pwestman/pwestman.github.io/Images/ghmain.JPG

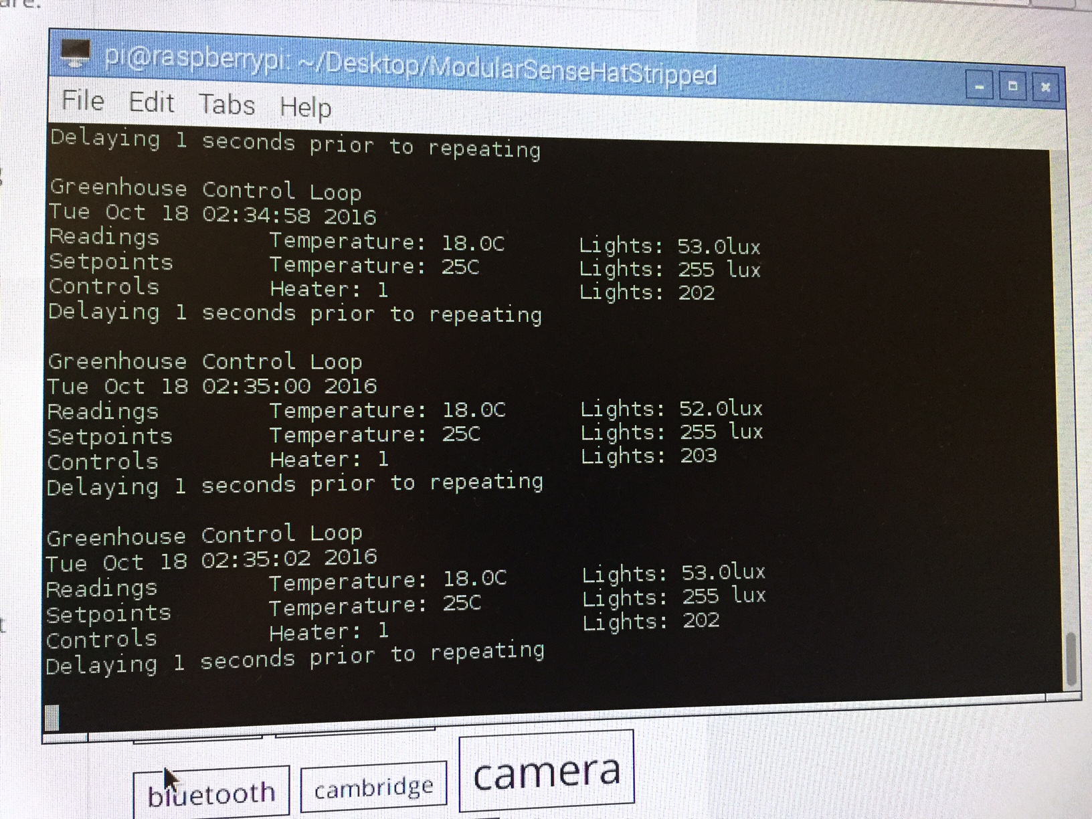
Images/ghmain.JPG
