pwestman/pwestman.github.io/Images/green.jpg

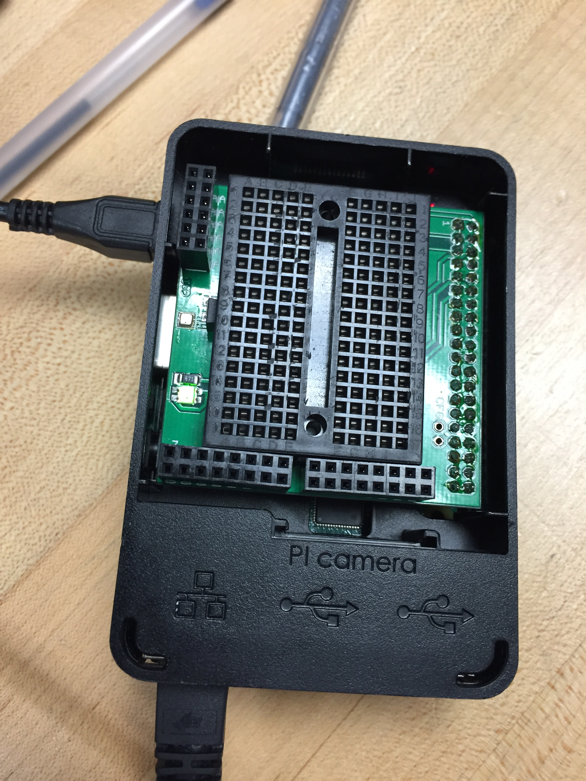
Images/green.jpg
