pwestman/pwestman.github.io/Images/greenLight.JPG

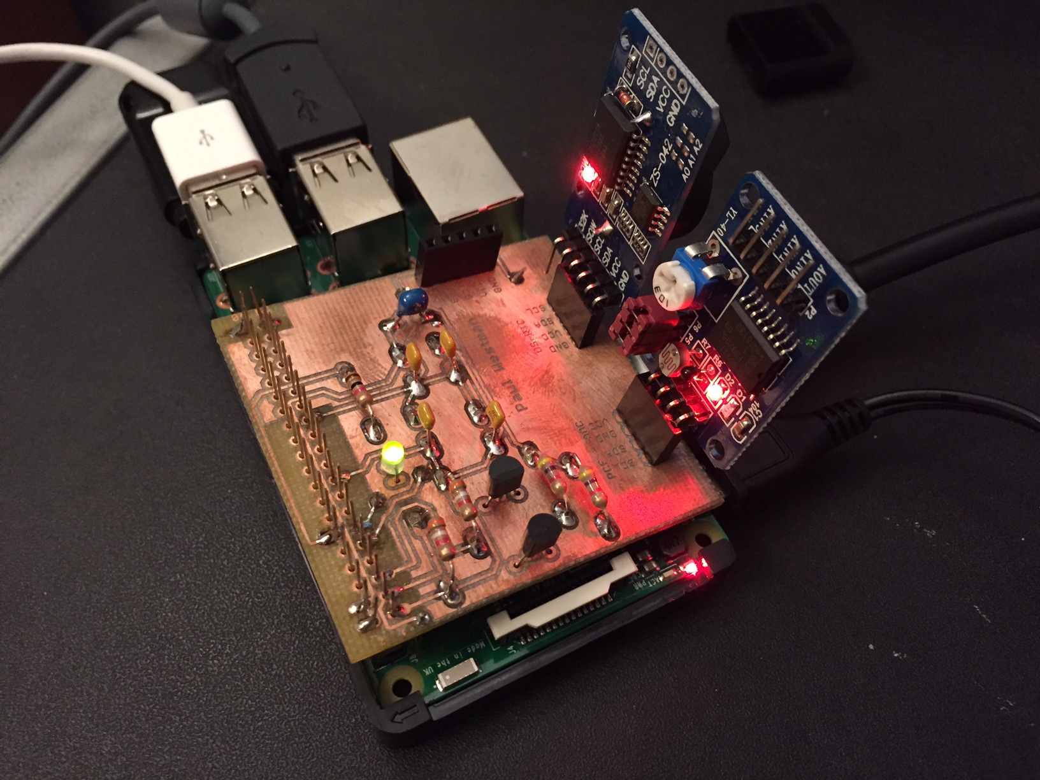
Images/greenLight.JPG
