pwestman/pwestman.github.io/Images/i2cdetect.JPG

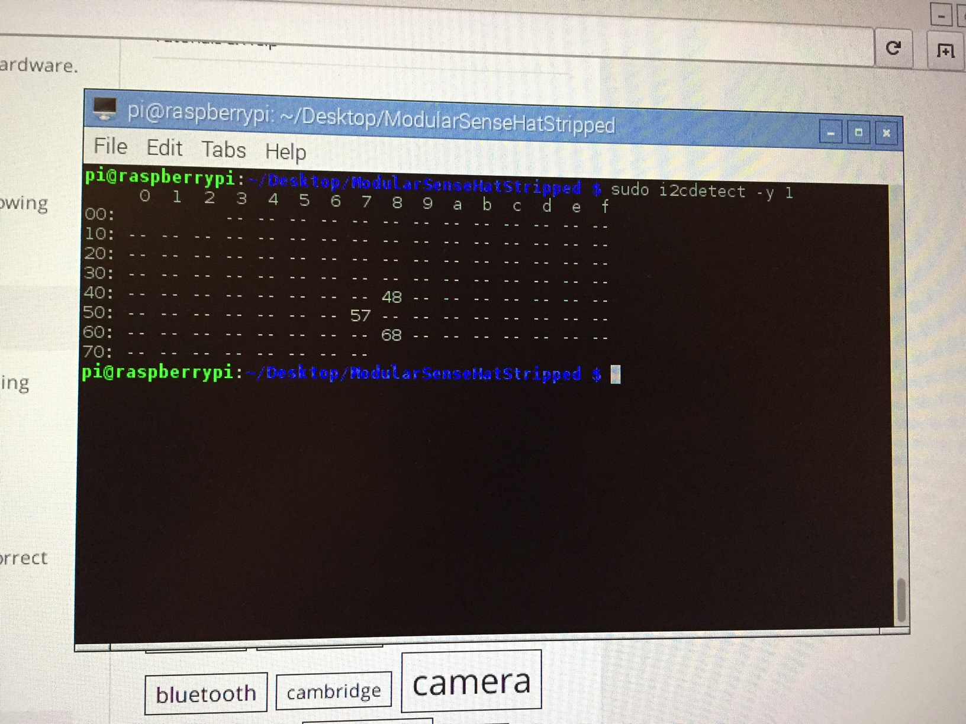
Images/i2cdetect.JPG
