pwestman/pwestman.github.io/Images/PCB.JPG

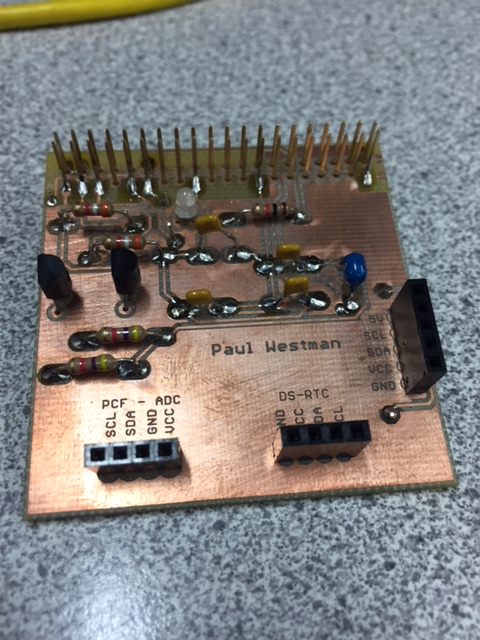
Images/PCB.JPG
