pwestman/pwestman.github.io/Images/traffic2B.JPG

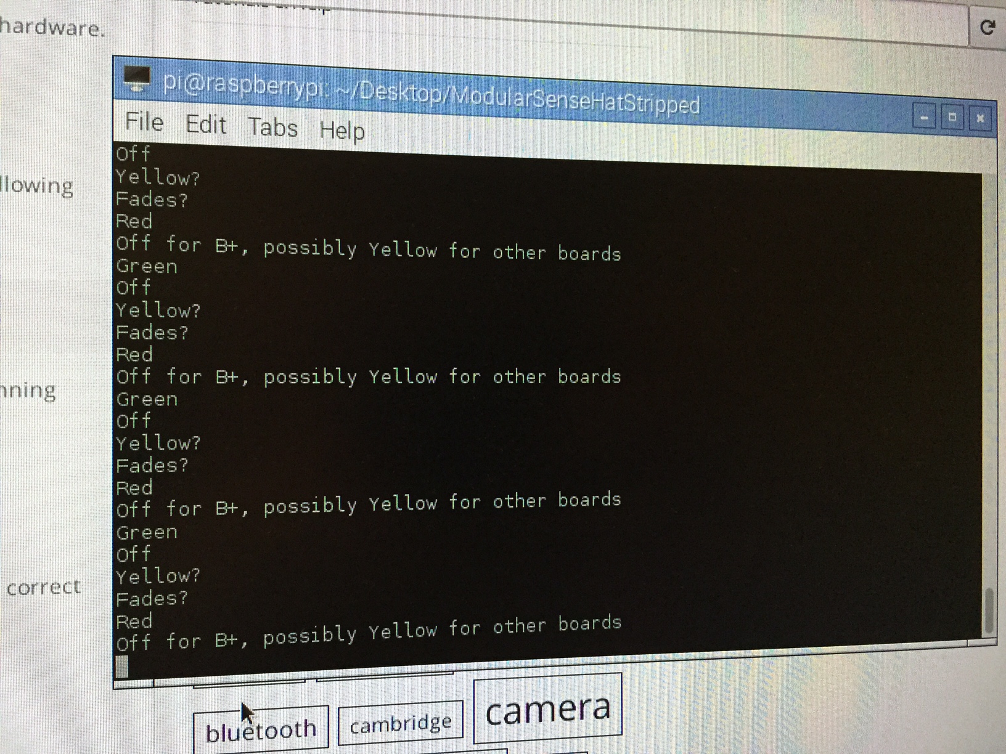
Images/traffic2B.JPG
