pwestman/pwestman.github.io/README.images/AcrylicScaleWalls.jpg

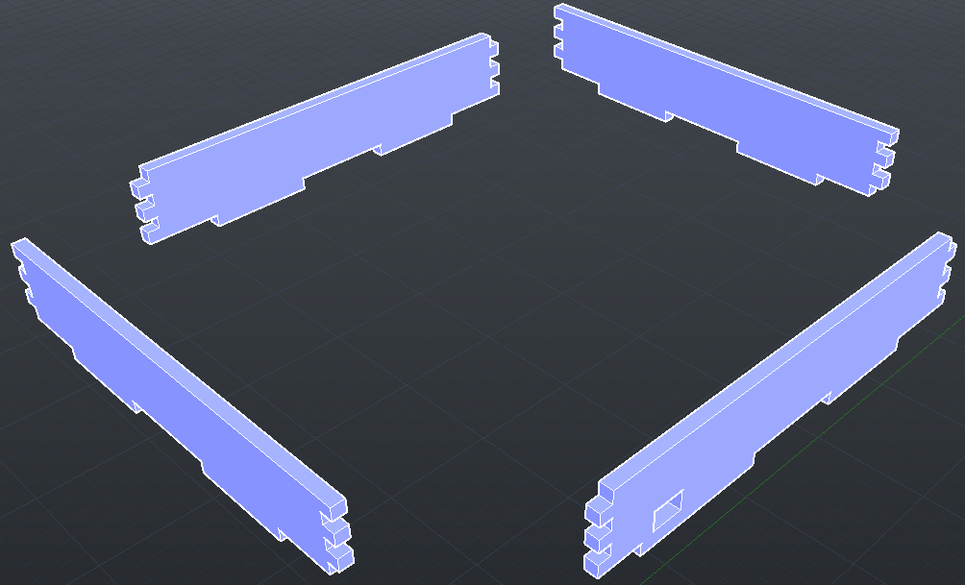
README.images/AcrylicScaleWalls.jpg
